ZTL-Space/Badge-Eule-/doc/detailed-docu-pics/IMG_0104.JPG

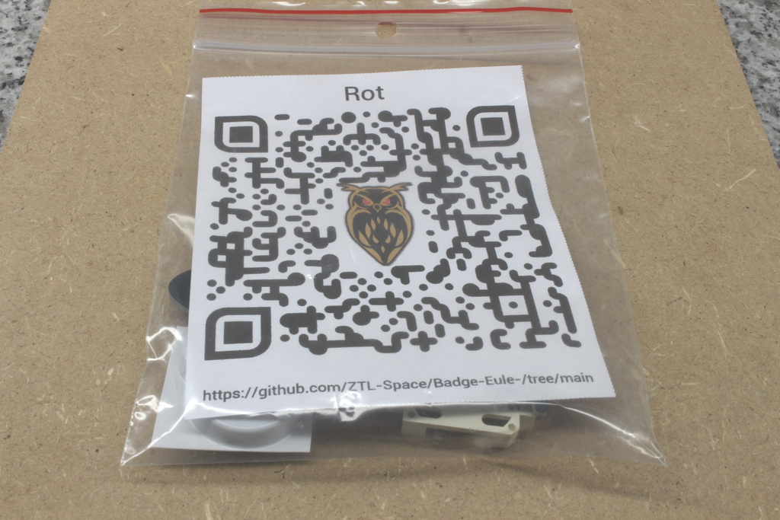
doc/detailed-docu-pics/IMG_0104.JPG
