ZTL-Space/Badge-Eule-/doc/detailed-docu-pics/IMG_0105.JPG

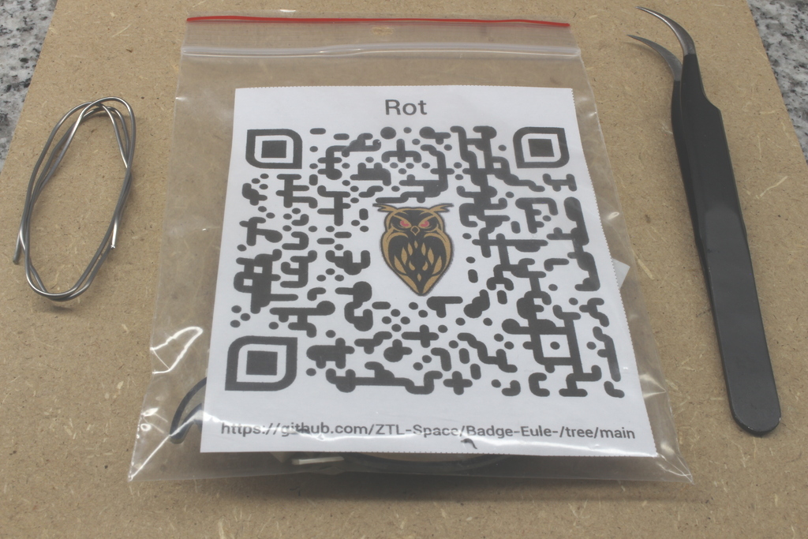
doc/detailed-docu-pics/IMG_0105.JPG
