ZTL-Space/Badge-Eule-/doc/detailed-docu-pics/IMG_0107.JPG

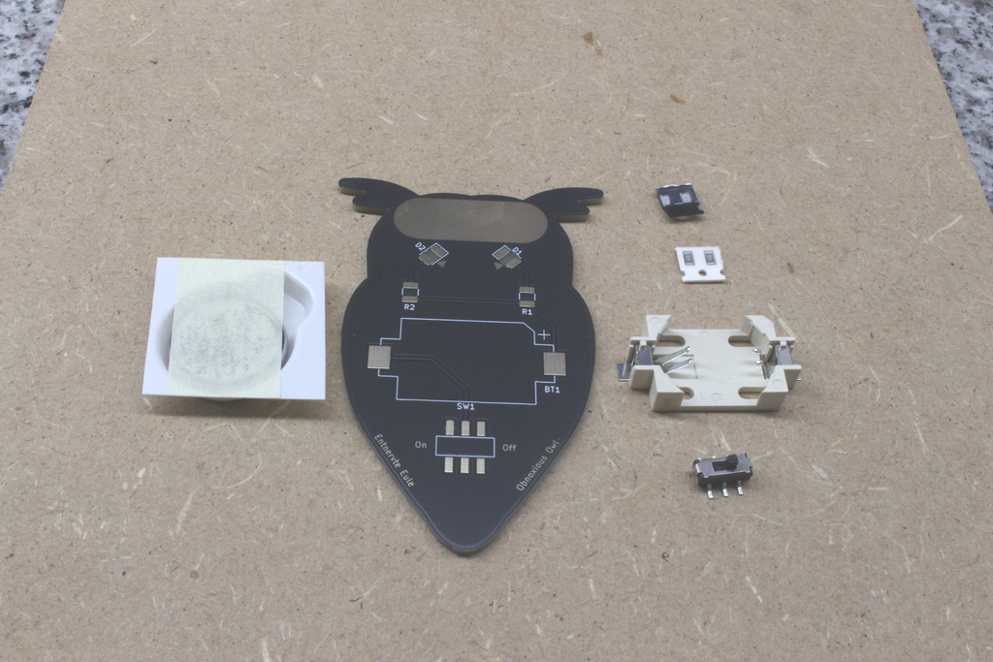
doc/detailed-docu-pics/IMG_0107.JPG
