ZTL-Space/Badge-Eule-/doc/detailed-docu-pics/IMG_0108.JPG

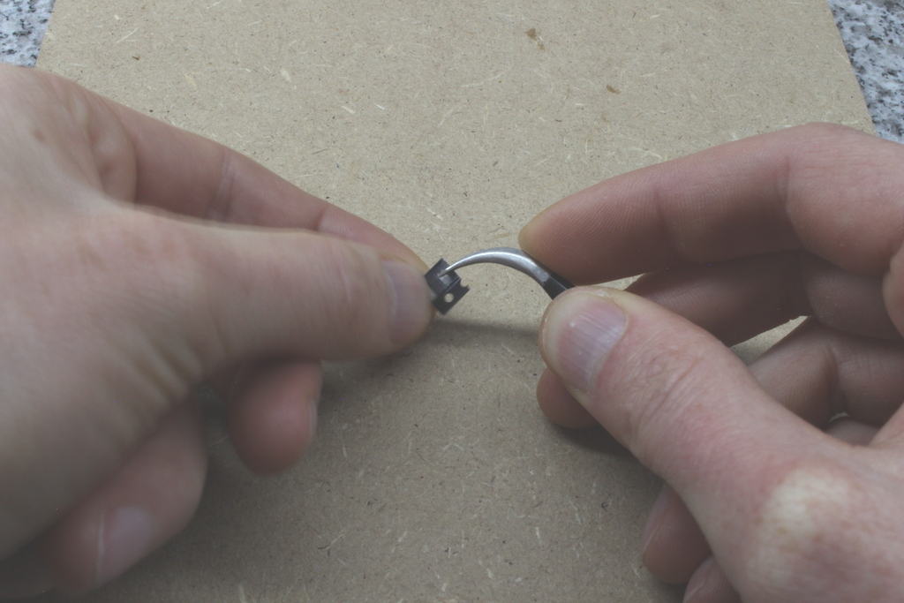
doc/detailed-docu-pics/IMG_0108.JPG
