ZTL-Space/Badge-Eule-/doc/detailed-docu-pics/IMG_0109.JPG

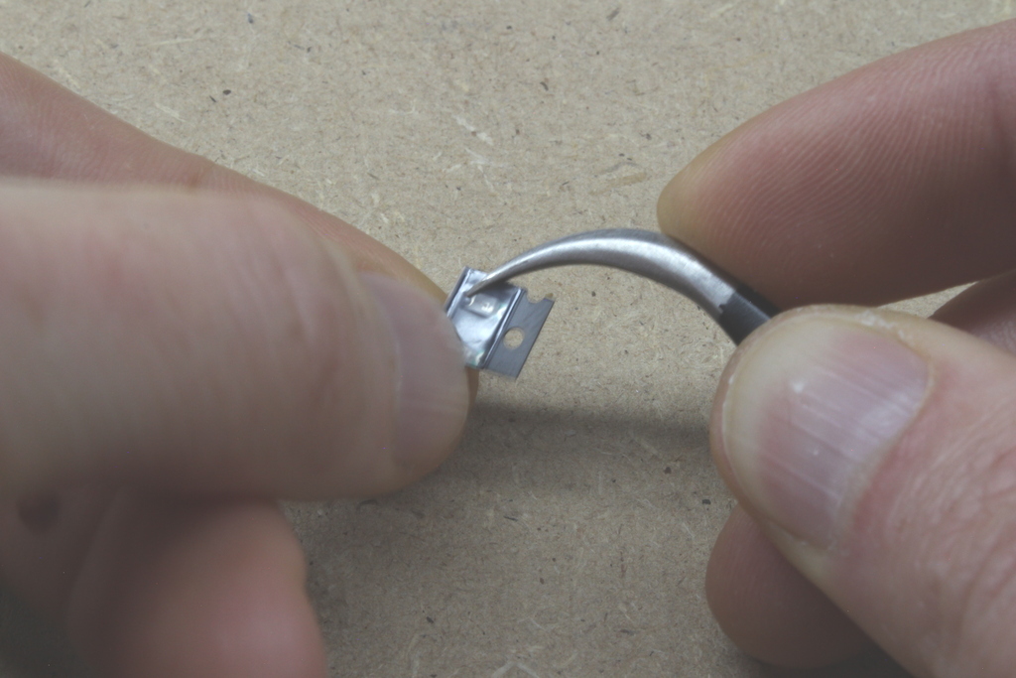
doc/detailed-docu-pics/IMG_0109.JPG
