ZTL-Space/Badge-Eule-/doc/detailed-docu-pics/IMG_0110.JPG

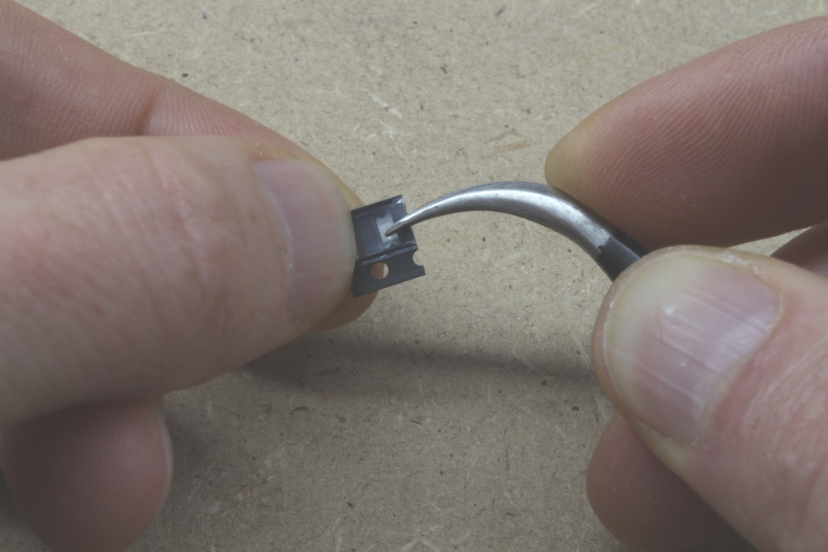
doc/detailed-docu-pics/IMG_0110.JPG
