ZTL-Space/Badge-Eule-/doc/detailed-docu-pics/IMG_0111.JPG

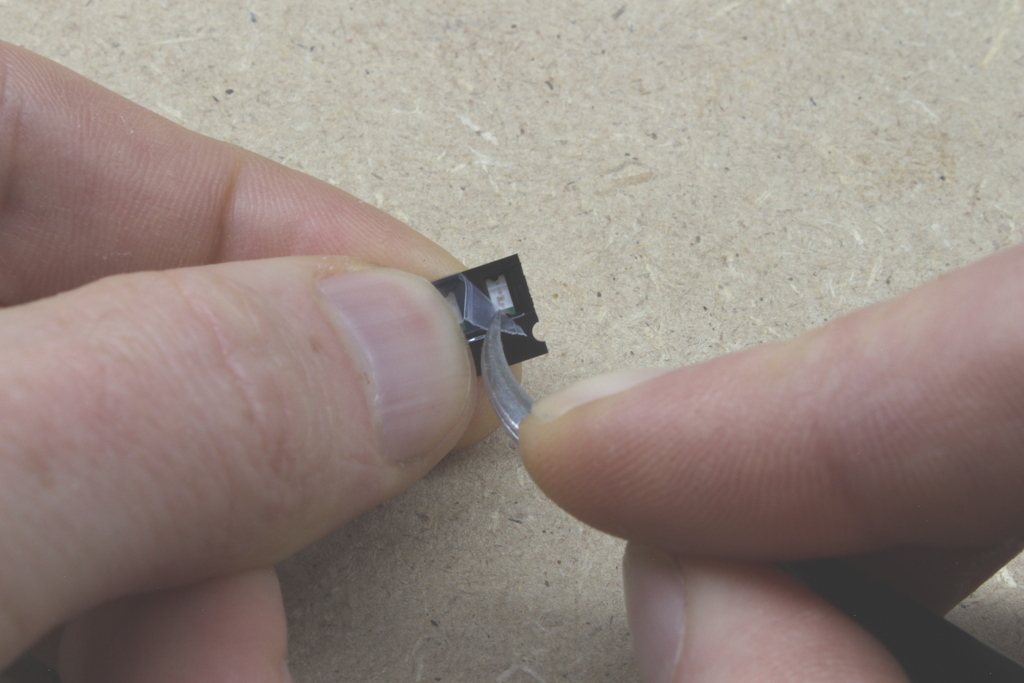
doc/detailed-docu-pics/IMG_0111.JPG
