ZTL-Space/Badge-Eule-/doc/detailed-docu-pics/IMG_0112.JPG

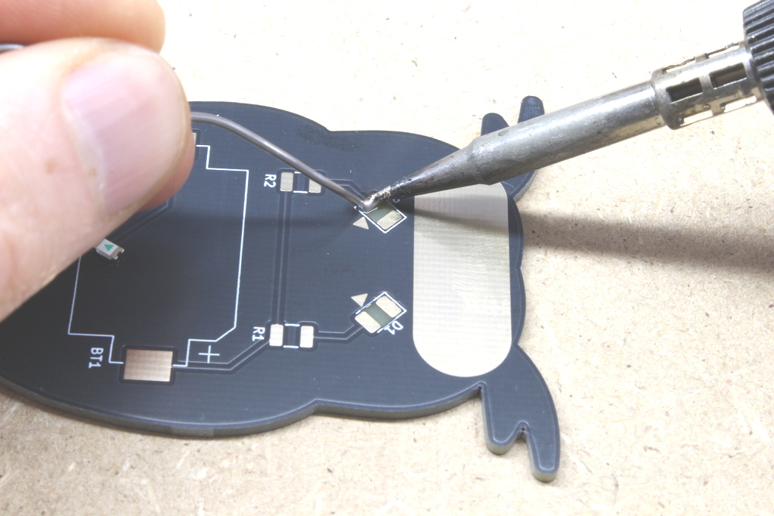
doc/detailed-docu-pics/IMG_0112.JPG
