ZTL-Space/Badge-Eule-/doc/detailed-docu-pics/IMG_0113.JPG

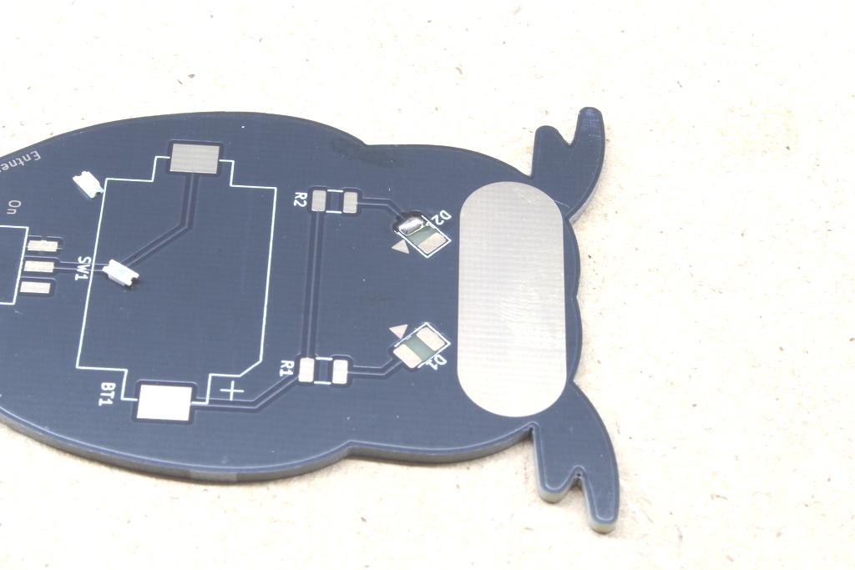
doc/detailed-docu-pics/IMG_0113.JPG
