ZTL-Space/Badge-Eule-/doc/detailed-docu-pics/IMG_0114.JPG

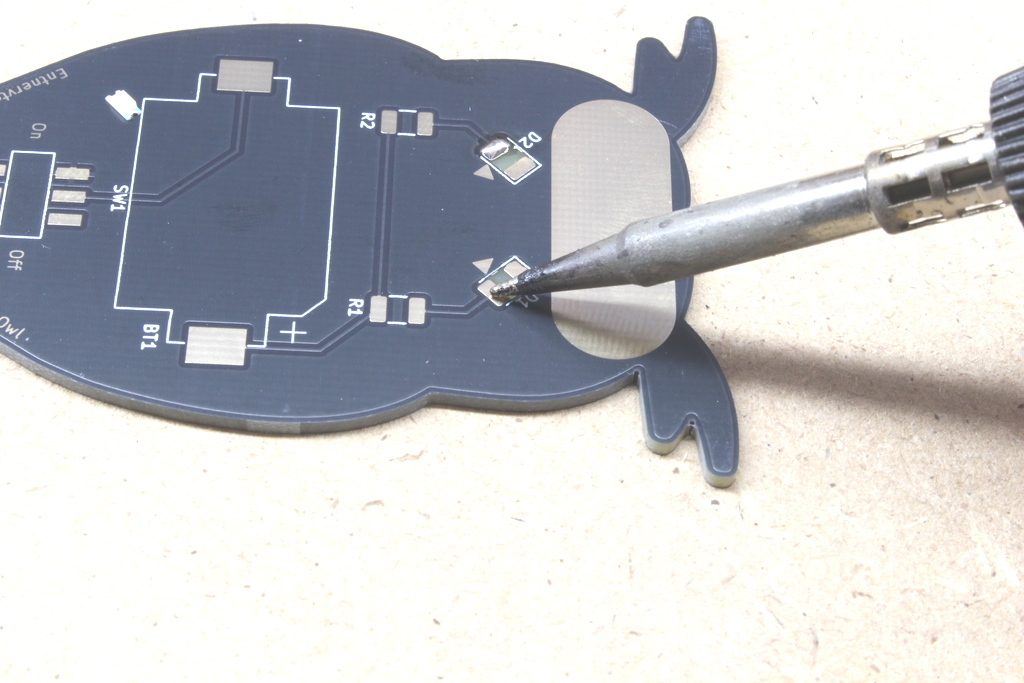
doc/detailed-docu-pics/IMG_0114.JPG
