ZTL-Space/Badge-Eule-/doc/detailed-docu-pics/IMG_0115.JPG

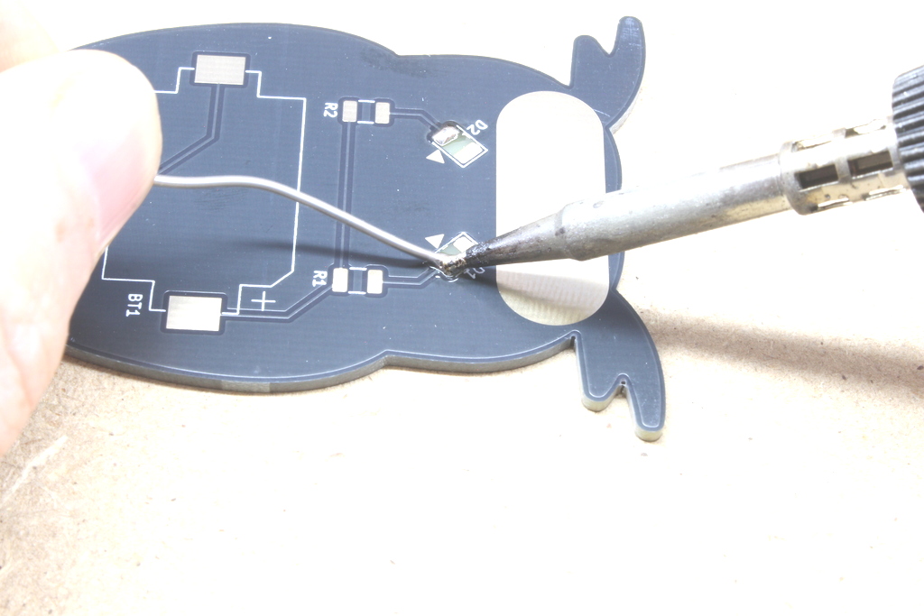
doc/detailed-docu-pics/IMG_0115.JPG
