ZTL-Space/Badge-Eule-/doc/detailed-docu-pics/IMG_0116.JPG

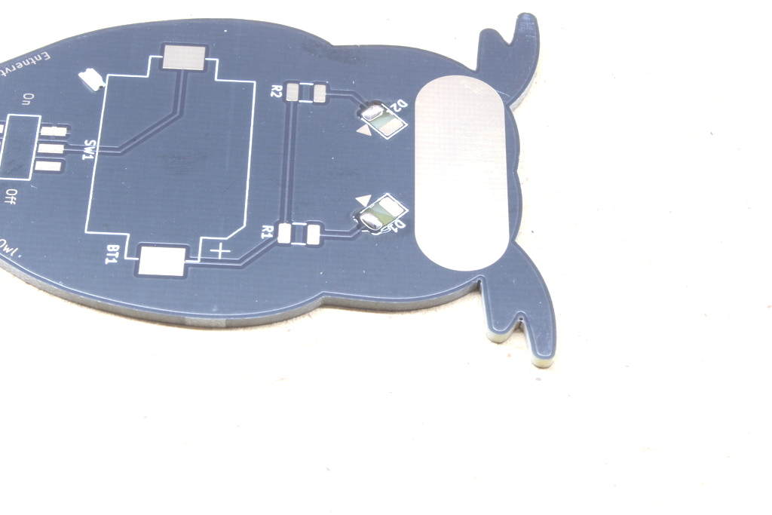
doc/detailed-docu-pics/IMG_0116.JPG
