ZTL-Space/Badge-Eule-/doc/detailed-docu-pics/IMG_0117.JPG

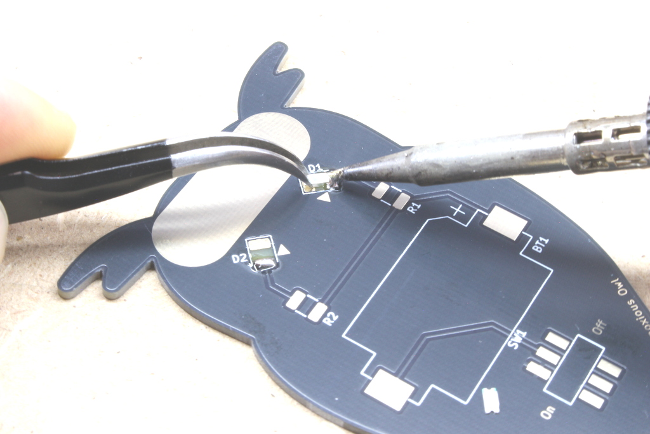
doc/detailed-docu-pics/IMG_0117.JPG
