ZTL-Space/Badge-Eule-/doc/detailed-docu-pics/IMG_0118.JPG

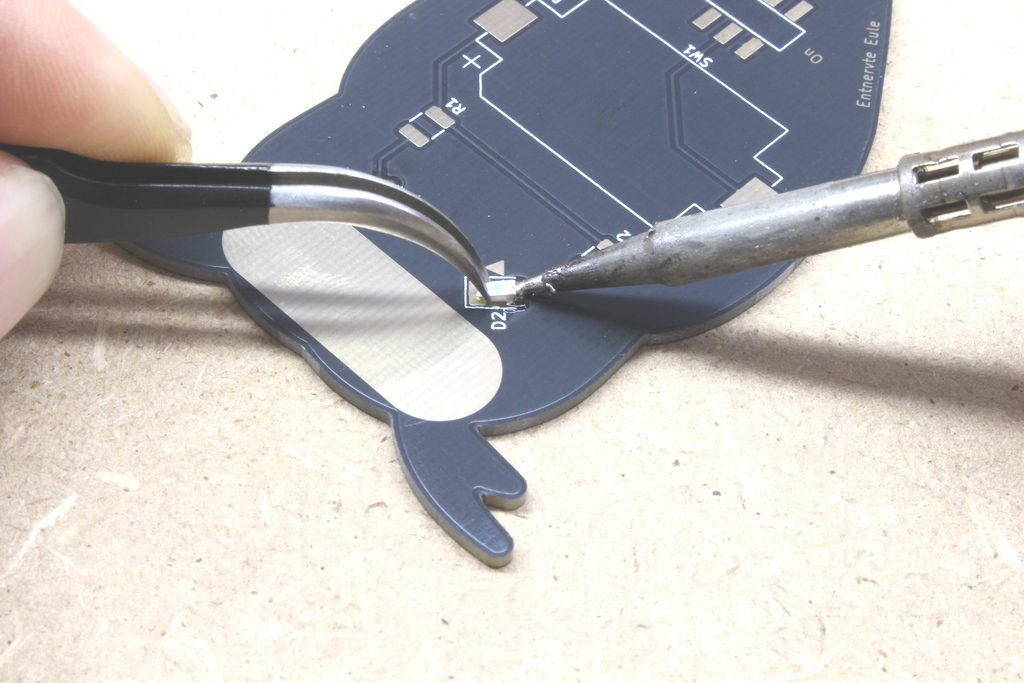
doc/detailed-docu-pics/IMG_0118.JPG
