ZTL-Space/Badge-Eule-/doc/detailed-docu-pics/IMG_0119.JPG

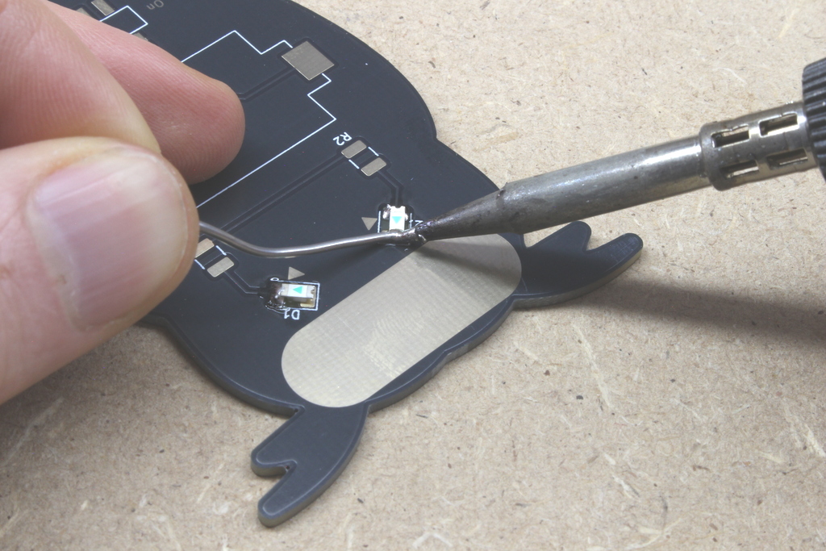
doc/detailed-docu-pics/IMG_0119.JPG
