ZTL-Space/Badge-Eule-/doc/detailed-docu-pics/IMG_0120.JPG

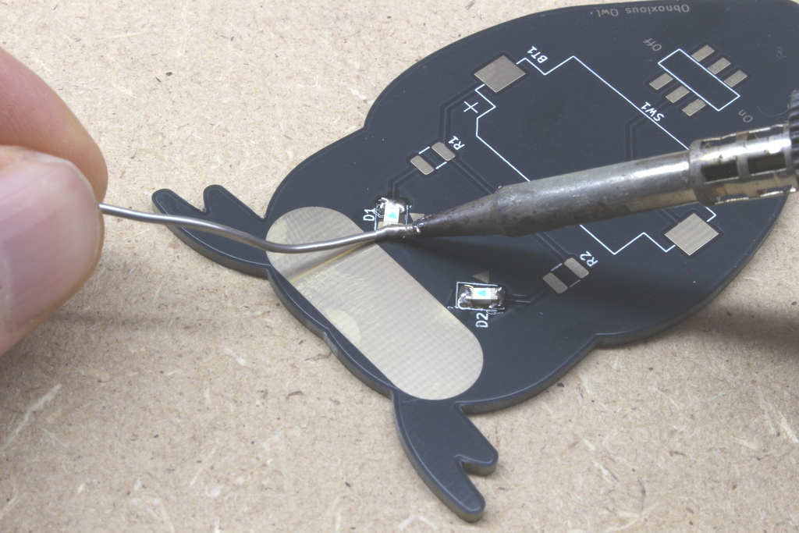
doc/detailed-docu-pics/IMG_0120.JPG
