ZTL-Space/Badge-Eule-/doc/detailed-docu-pics/IMG_0121.JPG

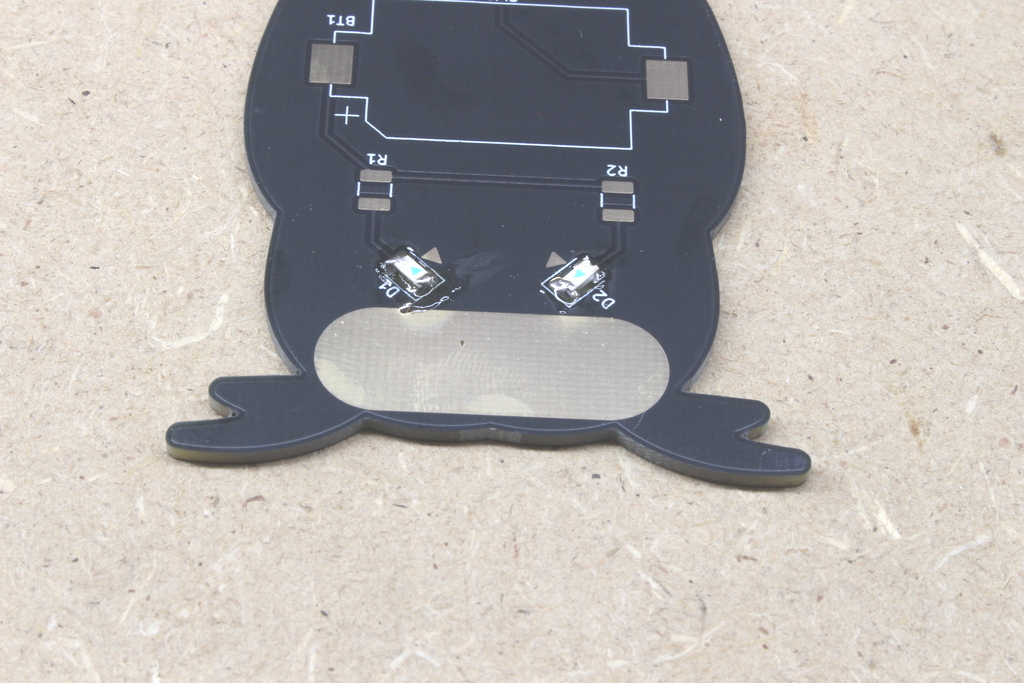
doc/detailed-docu-pics/IMG_0121.JPG
