ZTL-Space/Badge-Eule-/doc/detailed-docu-pics/IMG_0122.JPG

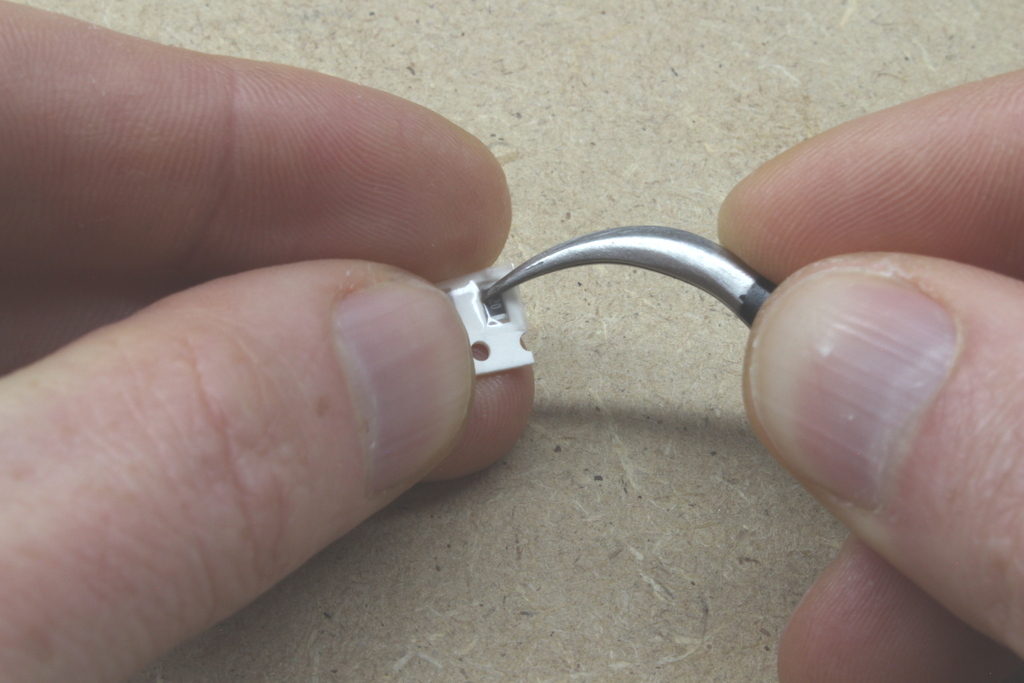
doc/detailed-docu-pics/IMG_0122.JPG
