ZTL-Space/Badge-Eule-/doc/detailed-docu-pics/IMG_0123.JPG

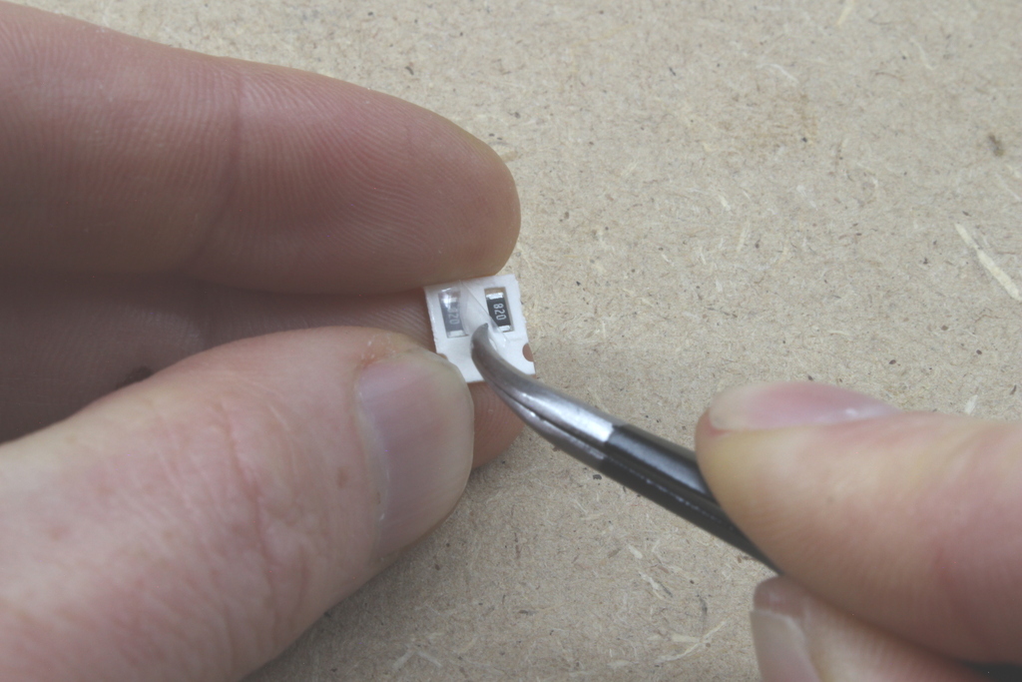
doc/detailed-docu-pics/IMG_0123.JPG
