ZTL-Space/Badge-Eule-/doc/detailed-docu-pics/IMG_0124.JPG

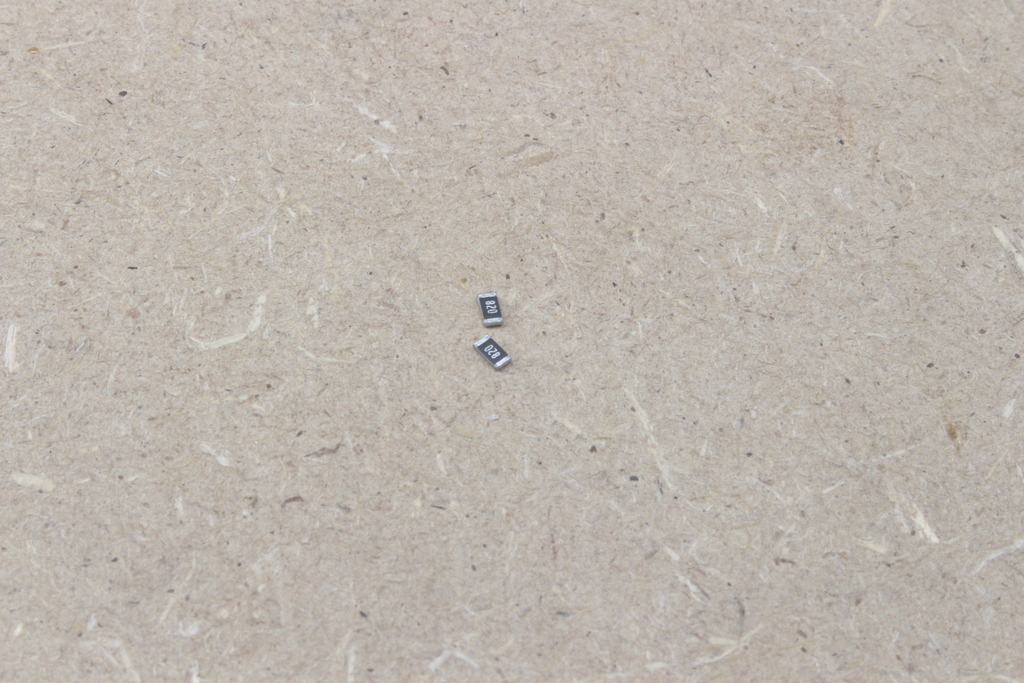
doc/detailed-docu-pics/IMG_0124.JPG
