ZTL-Space/Badge-Eule-/doc/detailed-docu-pics/IMG_0125.JPG

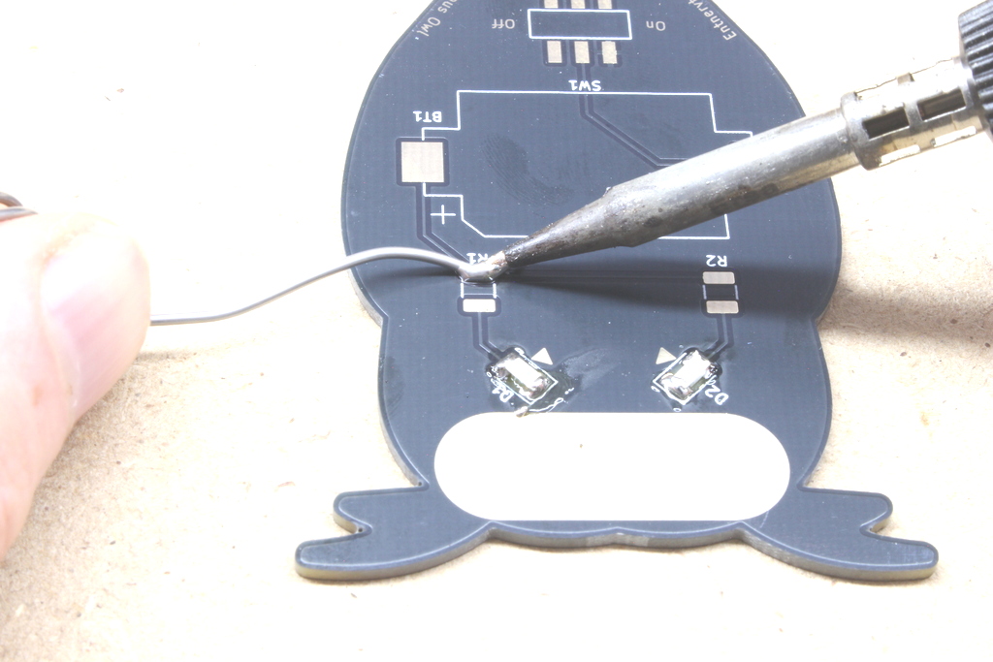
doc/detailed-docu-pics/IMG_0125.JPG
