ZTL-Space/Badge-Eule-/doc/detailed-docu-pics/IMG_0126.JPG

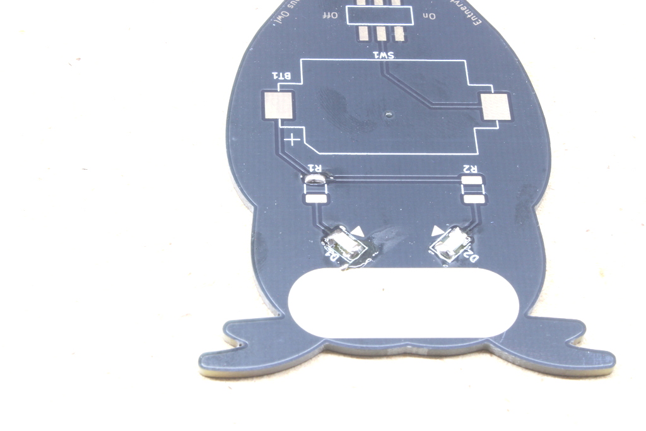
doc/detailed-docu-pics/IMG_0126.JPG
