ZTL-Space/Badge-Eule-/doc/detailed-docu-pics/IMG_0127.JPG

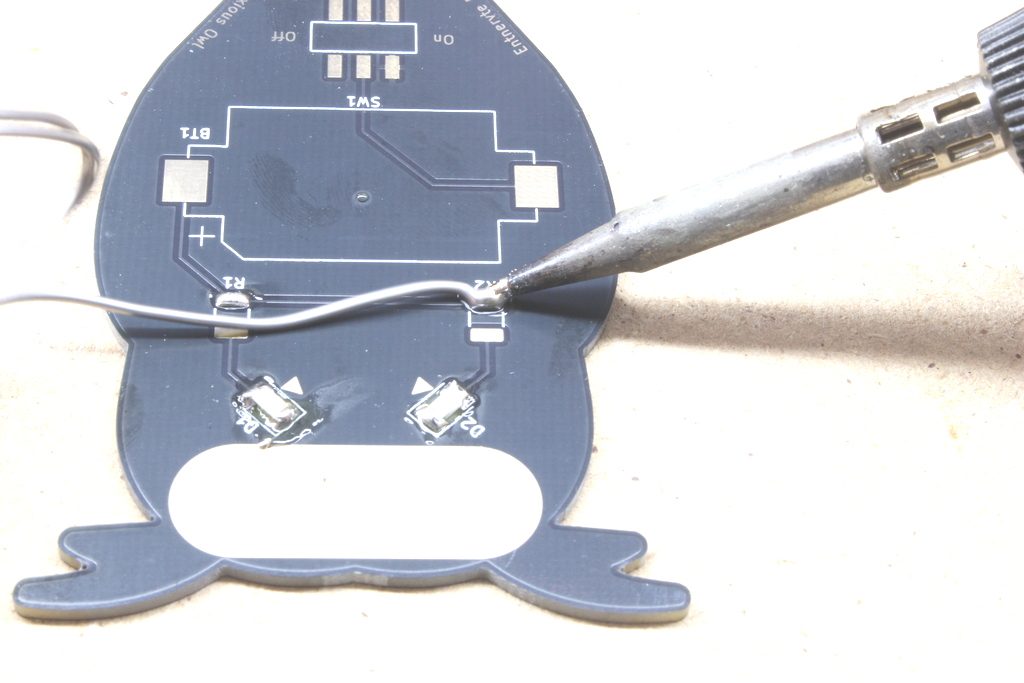
doc/detailed-docu-pics/IMG_0127.JPG
