ZTL-Space/Badge-Eule-/doc/detailed-docu-pics/IMG_0128.JPG

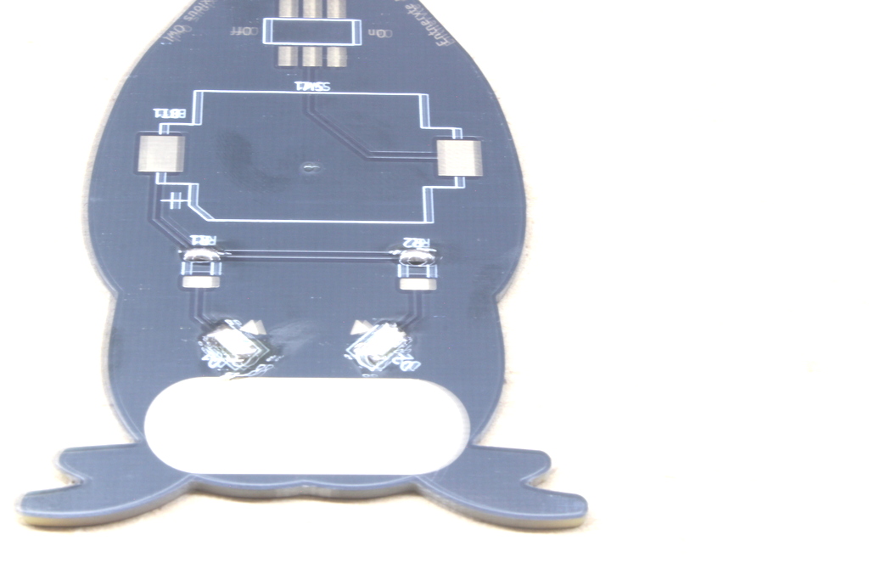
doc/detailed-docu-pics/IMG_0128.JPG
