ZTL-Space/Badge-Eule-/doc/detailed-docu-pics/IMG_0130.JPG

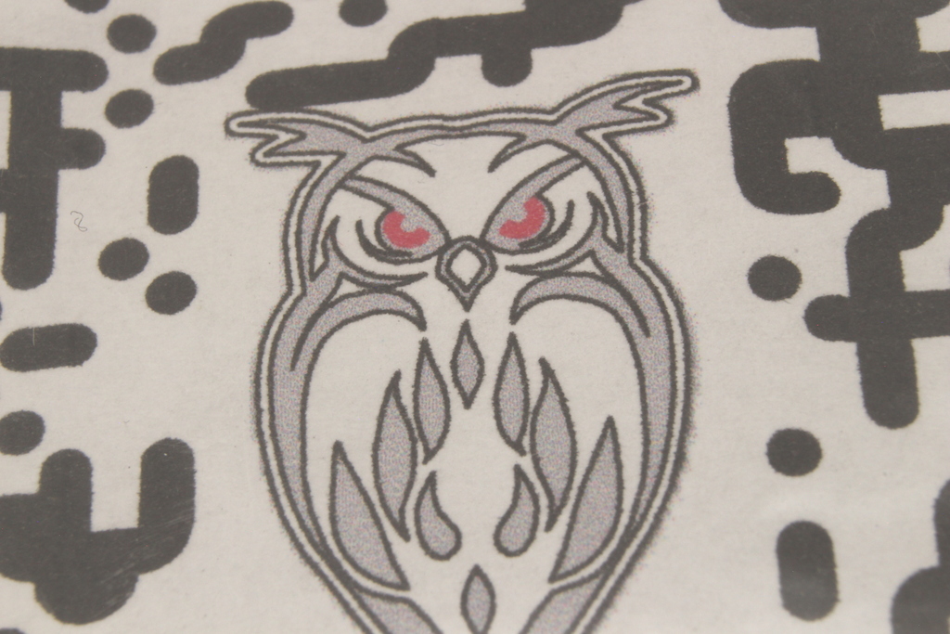
doc/detailed-docu-pics/IMG_0130.JPG
