ZTL-Space/Badge-Eule-/doc/detailed-docu-pics/IMG_0132.JPG

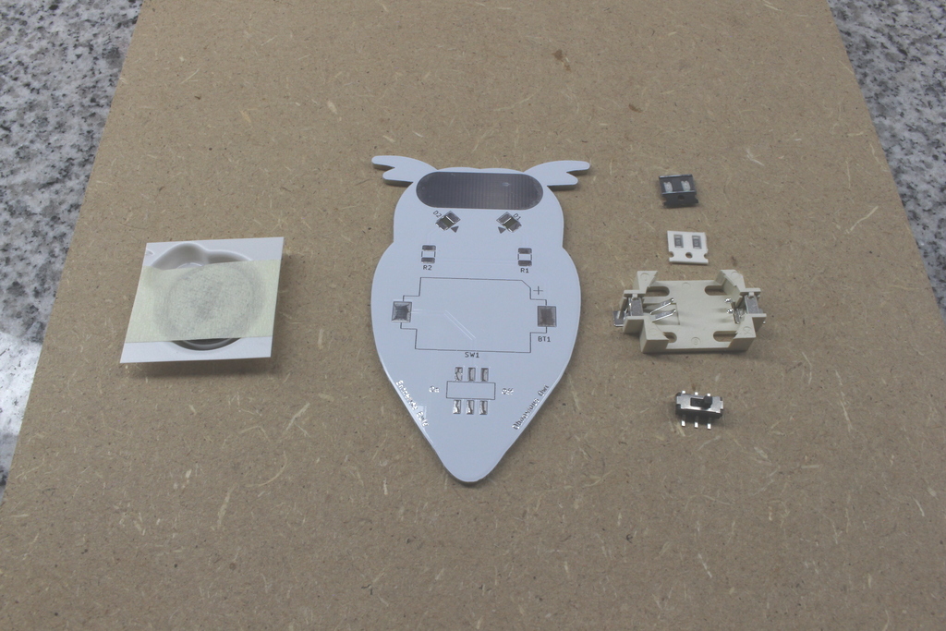
doc/detailed-docu-pics/IMG_0132.JPG
