ZTL-Space/Badge-Eule-/doc/detailed-docu-pics/IMG_0134.JPG

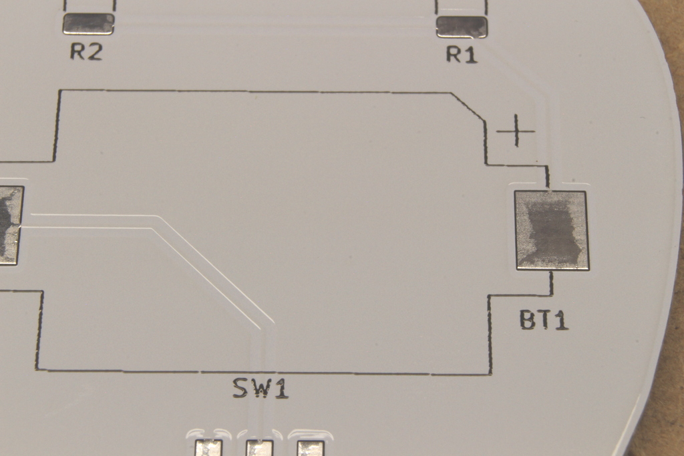
doc/detailed-docu-pics/IMG_0134.JPG
