ZTL-Space/Badge-Eule-/doc/detailed-docu-pics/IMG_0153.JPG

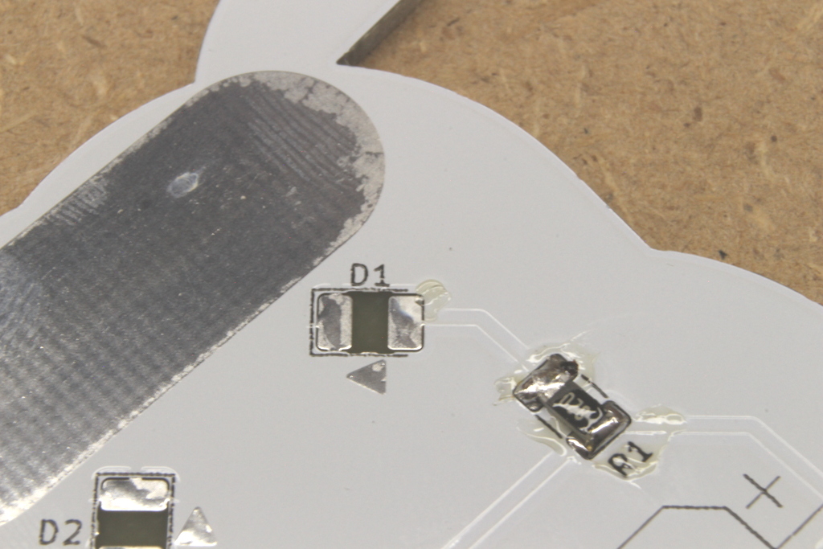
doc/detailed-docu-pics/IMG_0153.JPG
