ZTL-Space/Badge-Eule-/doc/detailed-docu-pics/IMG_0175.JPG

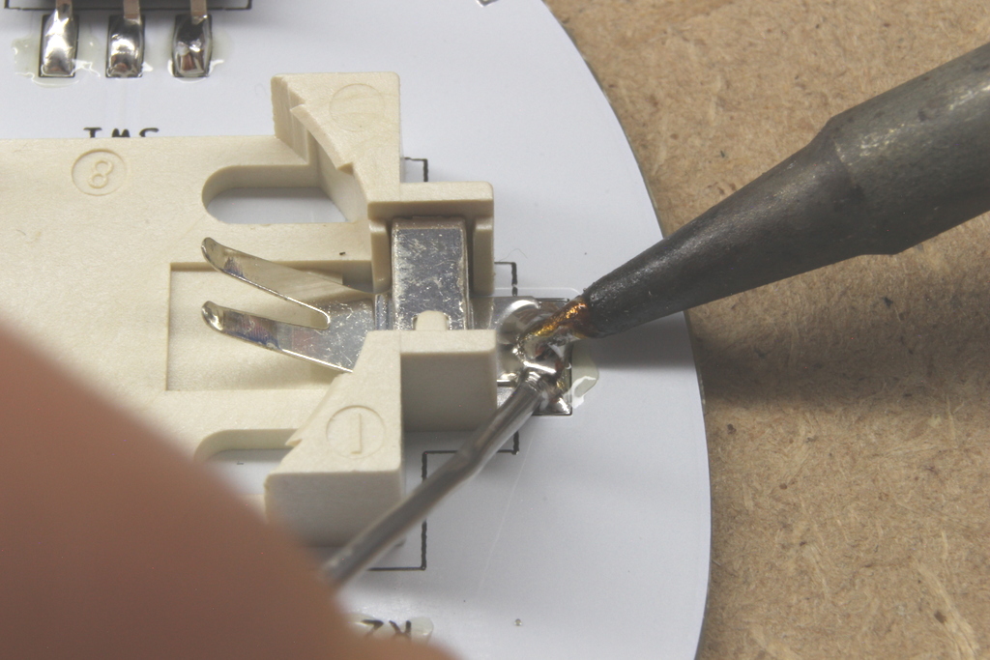
doc/detailed-docu-pics/IMG_0175.JPG
