ZTL-Space/Badge-Eule-/doc/detailed-docu-pics/IMG_0183.JPG

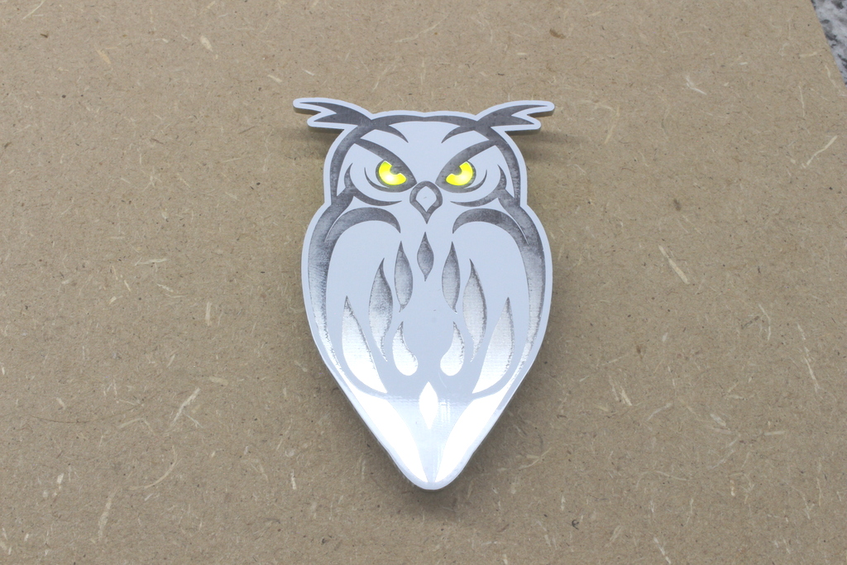
doc/detailed-docu-pics/IMG_0183.JPG
