ZTL-Space/Badge-Eule-/doc/docu-pics/01.jpg

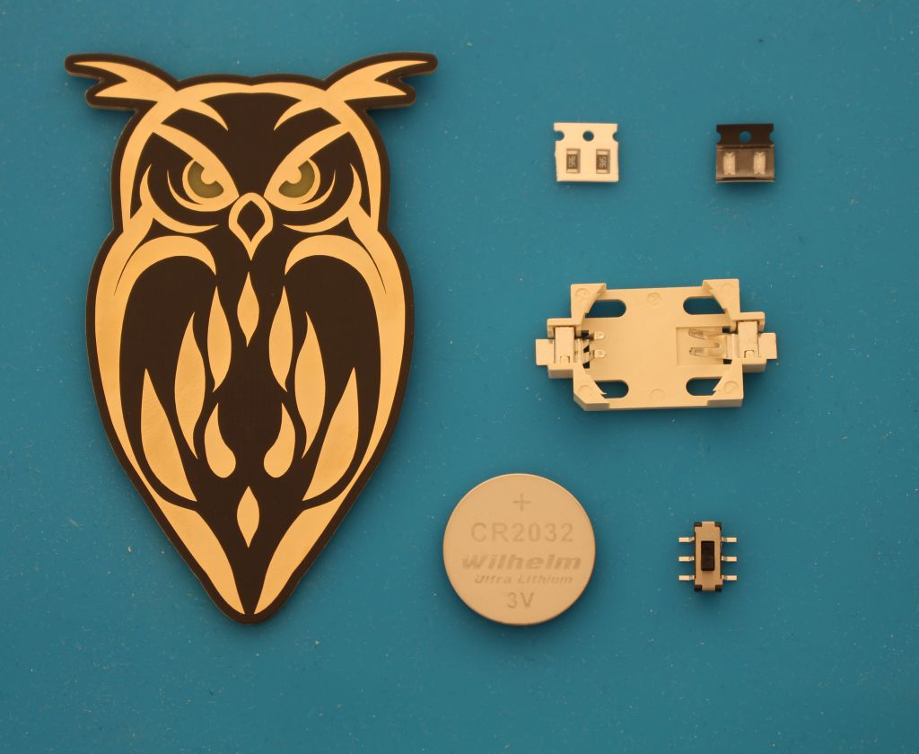
doc/docu-pics/01.jpg
